PrestoDL/Project_ESP32Controller/mpu6050_test/main/main.c

#include <stdio.h>
#include "freertos/FreeRTOS.h"
#include "freertos/task.h"
#include "esp_log.h"
#include "driver/i2c.h"
#include "mpu6050.h"

static const char *TAG = "MPU6050_EXAMPLE";

#define I2C_MASTER_SCL_IO           22
#define I2C_MASTER_SDA_IO           21
#define I2C_MASTER_NUM              I2C_NUM_0
#define I2C_MASTER_FREQ_HZ          400000
#define I2C_MASTER_TX_BUF_DISABLE   0
#define I2C_MASTER_RX_BUF_DISABLE   0

static mpu6050_handle_t mpu6050 = NULL;

static esp_err_t i2c_master_init(void)
{
    int i2c_master_port = I2C_MASTER_NUM;
    i2c_config_t conf = {
        .mode = I2C_MODE_MASTER,
        .sda_io_num = I2C_MASTER_SDA_IO,
        .scl_io_num = I2C_MASTER_SCL_IO,
        .sda_pullup_en = GPIO_PULLUP_ENABLE,
        .scl_pullup_en = GPIO_PULLUP_ENABLE,
        .master.clk_speed = I2C_MASTER_FREQ_HZ,
    };
    esp_err_t err = i2c_param_config(i2c_master_port, &conf);
    if (err != ESP_OK) {
        return err;
    }
    return i2c_driver_install(i2c_master_port, conf.mode, I2C_MASTER_RX_BUF_DISABLE, I2C_MASTER_TX_BUF_DISABLE, 0);
}

void app_main(void)
{
    ESP_ERROR_CHECK(i2c_master_init());
    ESP_LOGI(TAG, "I2C initialized successfully");

    mpu6050 = mpu6050_create(I2C_MASTER_NUM, MPU6050_I2C_ADDRESS);
    if (mpu6050 == NULL) {
        ESP_LOGE(TAG, "Failed to create MPU6050 device");
        return;
    }
    ESP_ERROR_CHECK(mpu6050_config(mpu6050, ACCE_FS_4G, GYRO_FS_500DPS));
    ESP_ERROR_CHECK(mpu6050_wake_up(mpu6050));

    while (1) {
        mpu6050_acce_value_t acce;

        esp_err_t err = mpu6050_get_acce(mpu6050, &acce);
        if (err == ESP_OK) {
            ESP_LOGI(TAG, "Acceleration X: %.2f g, Y: %.2f g, Z: %.2f g", acce.acce_x, acce.acce_y, acce.acce_z);
        } else {
            ESP_LOGE(TAG, "Failed to get accelerometer data");
        }
        
        vTaskDelay(pdMS_TO_TICKS(1000));
    }

    mpu6050_delete(mpu6050);
    ESP_ERROR_CHECK(i2c_driver_delete(I2C_MASTER_NUM));
}



/*
#include <stdio.h>
#include "freertos/FreeRTOS.h"
#include "freertos/task.h"
#include "driver/i2c.h"
#include "esp_log.h"

#define I2C_MASTER_SCL_IO           22
#define I2C_MASTER_SDA_IO           21
#define I2C_MASTER_NUM              I2C_NUM_0
#define I2C_MASTER_FREQ_HZ          100000
#define I2C_MASTER_TX_BUF_DISABLE   0
#define I2C_MASTER_RX_BUF_DISABLE   0

static const char *TAG = "I2C_SCANNER";

void app_main(void)
{
    i2c_config_t conf = {
        .mode = I2C_MODE_MASTER,
        .sda_io_num = I2C_MASTER_SDA_IO,
        .scl_io_num = I2C_MASTER_SCL_IO,
        .sda_pullup_en = GPIO_PULLUP_ENABLE,
        .scl_pullup_en = GPIO_PULLUP_ENABLE,
        .master.clk_speed = I2C_MASTER_FREQ_HZ,
    };
    i2c_param_config(I2C_MASTER_NUM, &conf);
    i2c_driver_install(I2C_MASTER_NUM, conf.mode, I2C_MASTER_RX_BUF_DISABLE, I2C_MASTER_TX_BUF_DISABLE, 0);

    ESP_LOGI(TAG, "Scanning I2C bus...");
    uint8_t address;
    for (address = 1; address < 127; address++) {
        i2c_cmd_handle_t cmd = i2c_cmd_link_create();
        i2c_master_start(cmd);
        i2c_master_write_byte(cmd, (address << 1) | I2C_MASTER_WRITE, true);
        i2c_master_stop(cmd);
        esp_err_t ret = i2c_master_cmd_begin(I2C_MASTER_NUM, cmd, pdMS_TO_TICKS(50));
        i2c_cmd_link_delete(cmd);

        if (ret == ESP_OK) {
            ESP_LOGI(TAG, "Found device at address 0x%02X", address);
        }
    }
    i2c_driver_delete(I2C_MASTER_NUM);
}
*/
